stanleyseow/ArduinoTracker-MicroAPRS/config.h

// config file to defines callsign, ssid, symbols and home location
#define MYCALL "NOCALL"
#define CALL_SSID 9
// Refer to http://wa8lmf.net/aprs/APRS_symbols.htm
#define SYMBOL_CHAR '('         // Blue Dot
#define SYMBOL_TABLE 's'        // Primary Table (s) or Alternate Table (a)
// Define your home lat & lon below
// http://andrew.hedges.name/experiments/convert_lat_long/
// Goto aprs.fi and find your deg mm.mm ( leave the secs blank )
// home
const float HOME_LAT = 3.16925;
const float HOME_LON = 101.64972;
//
//
// Custom Comments here
#define COMMENT ""
